pdaehne/Atari-A8-Cartridge/images/Xgpro_Program_Slot1.png

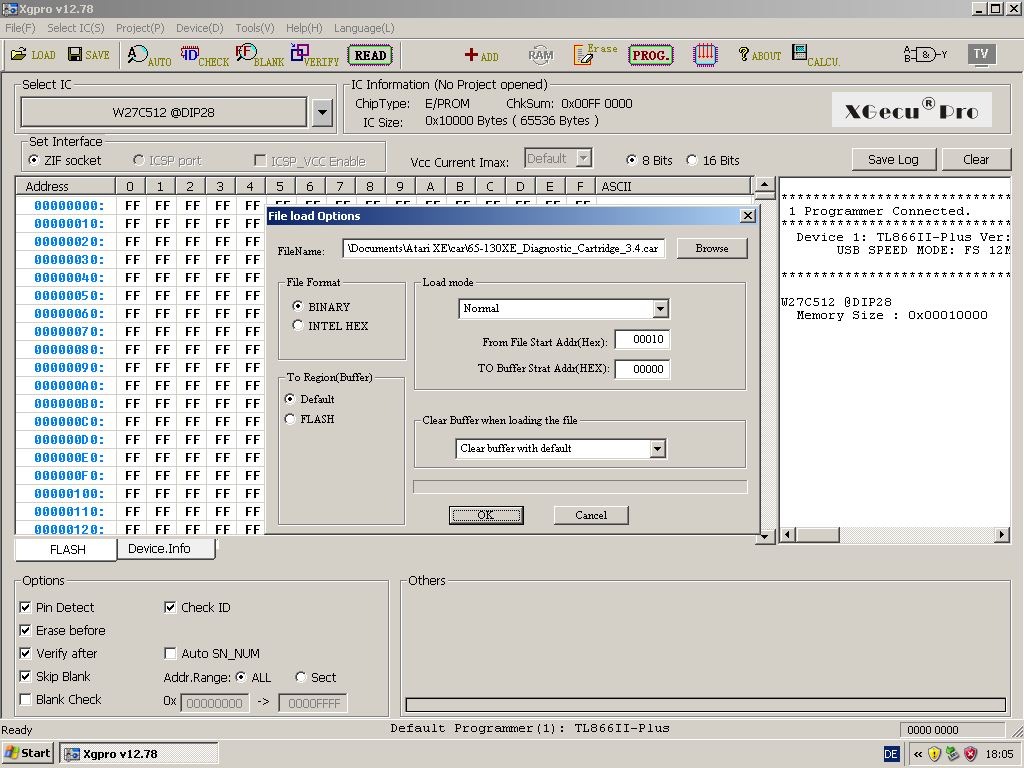
images/Xgpro_Program_Slot1.png
